f-ranek/moto-beam-driver/electrical/interface_module.kicad_sch

## KiCad design electrical/interface_module.kicad_sch (2024-03-23)

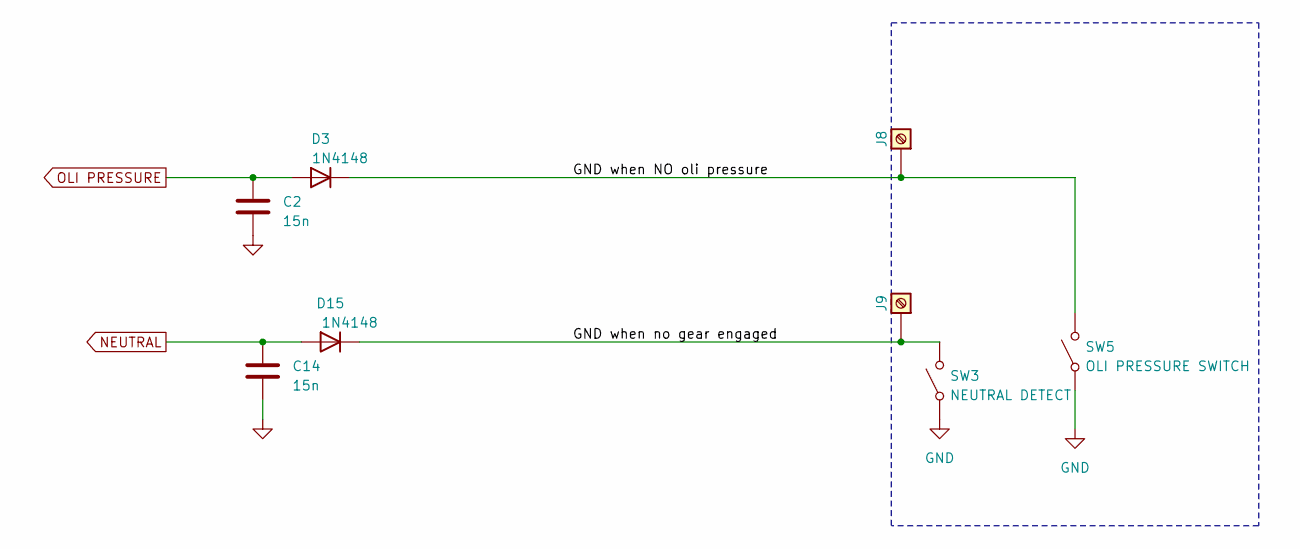
[picture p6: schematic interface_module.kicad_sch]

Parts:
C2, C14: 15n
D3, D15: 1N4148; D_DO-35_SOD27_P7.62mm_Horizontal
J8, J9: Screw_Terminal_01x01
SW3: NEUTRAL DETECT
SW5: OLI PRESSURE SWITCH

Connections:
GND: C2.2, C14.2, SW3.1 (A), SW5.1 (A)
GND when NO oli pressure: D3.1 (K), J8.1, SW5.2 (B)
GND when no gear engaged: D15.1 (K), J9.1, SW3.2 (B)
NEUTRAL: C14.1, D15.2 (A)
OLI PRESSURE: C2.1, D3.2 (A)
