f-ranek/moto-beam-driver/electrical/power_delivery_module.kicad_sch

## KiCad design electrical/power_delivery_module.kicad_sch (2024-04-14)

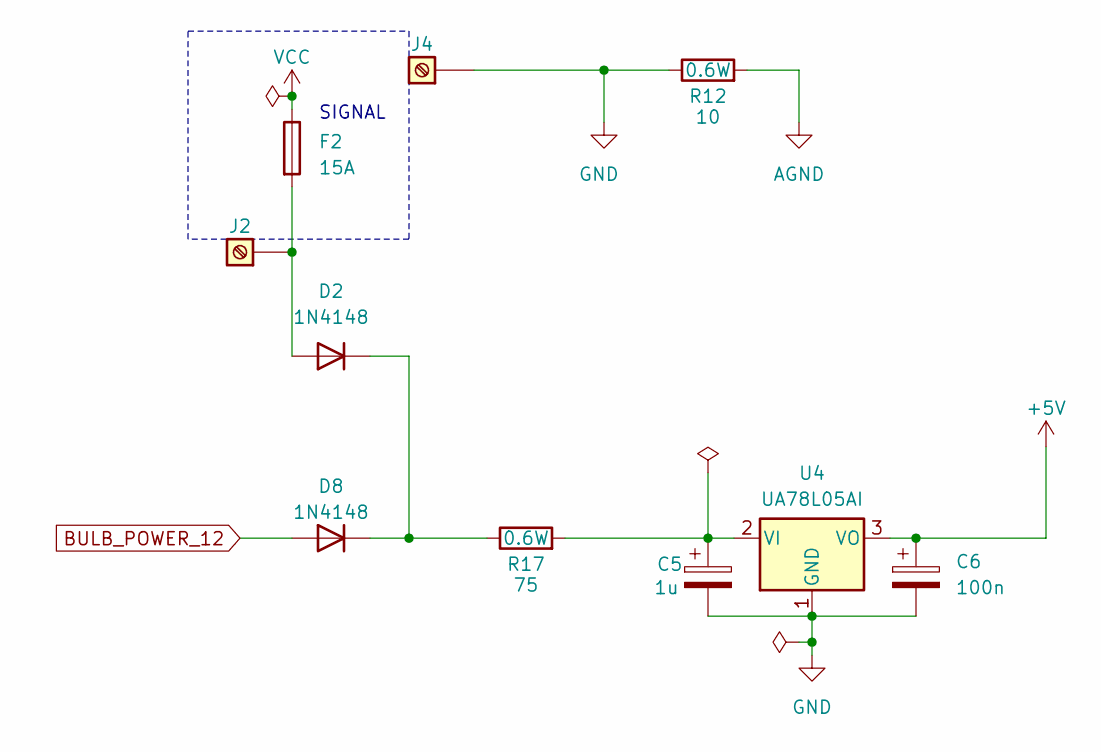
[picture p7: schematic power_delivery_module.kicad_sch]

Parts:
C5: 1u; D_DO-35_SOD27_P7.62mm_Horizontal
C6: 100n; D_DO-35_SOD27_P7.62mm_Horizontal
D2, D8: 1N4148; D_DO-41_SOD81_P10.16mm_Horizontal
F2: 15A
J2, J4: Screw_Terminal_01x01
R12: 10
R17: 75
U4: UA78L05AI; TO-220-3_Vertical

Connections:
+5V: C6.1, U4.3 (VO)
AGND: R12.2
BULB_POWER_12: D8.2 (A)
GND: C5.2, C6.2, J4.1, R12.1, U4.1 (GND)
unnamed: C5.1, R17.2, U4.2 (VI)
unnamed: D2.1 (K), D8.1 (K), R17.1
unnamed: D2.2 (A), F2.2, J2.1
VCC: F2.1

Notes on the sheet:
SIGNAL
