f-ranek/moto-beam-driver/electrical/power_module_n.kicad_sch

## KiCad design electrical/power_module_n.kicad_sch (2024-04-14)

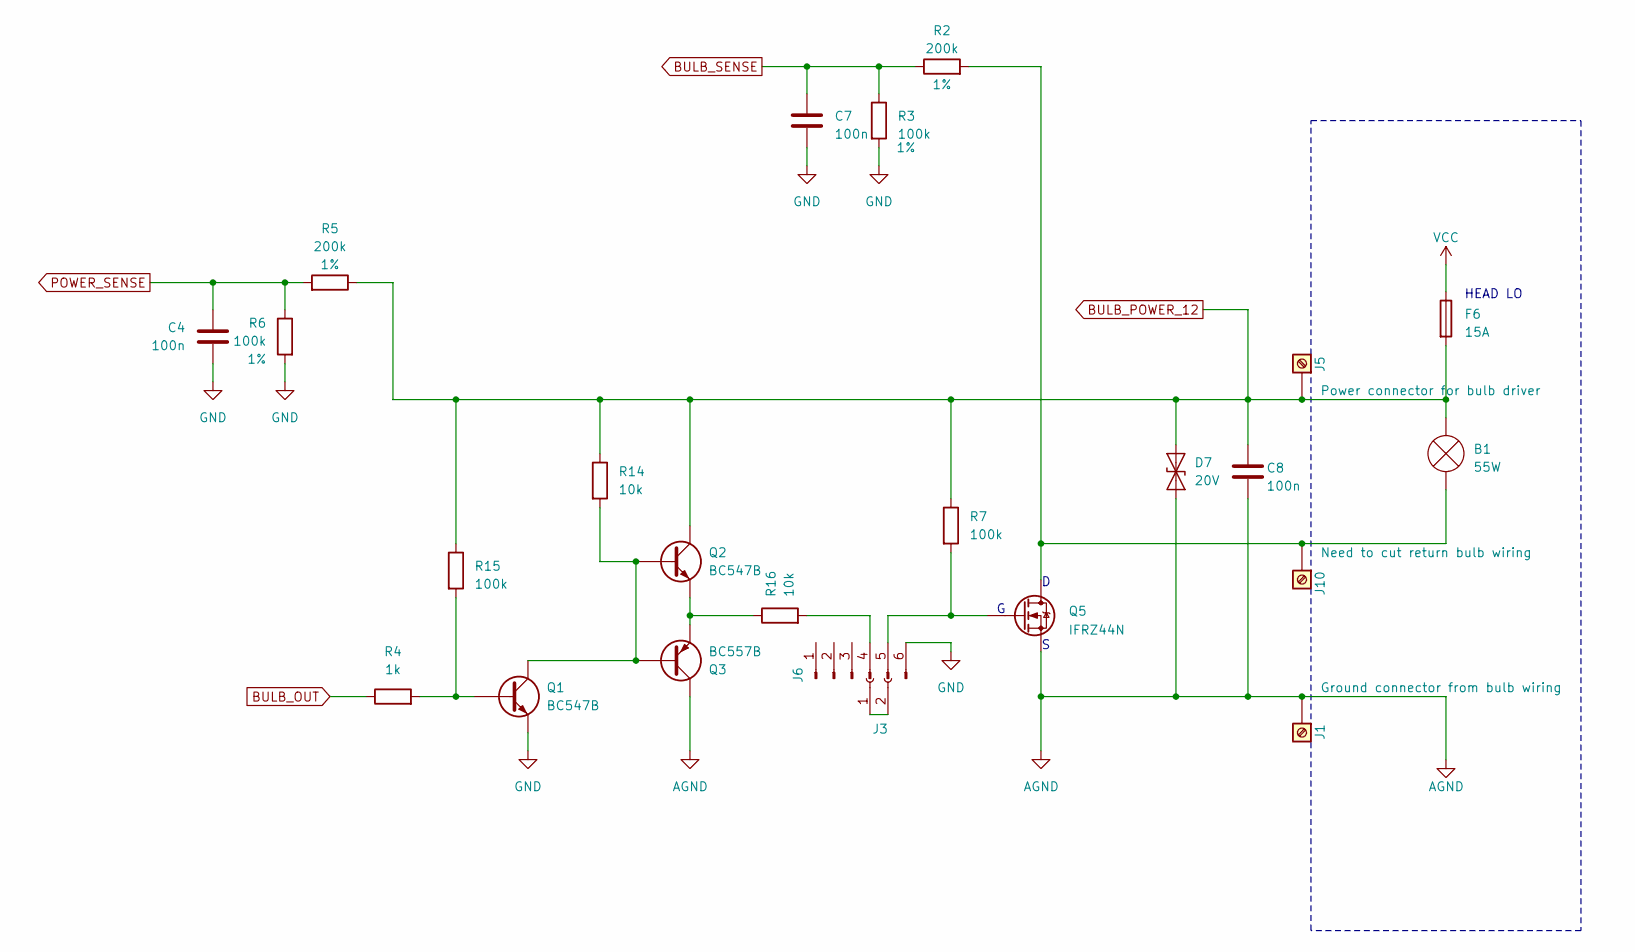
[picture p8: schematic power_module_n.kicad_sch]

Parts:
B1: 55W
C4, C7, C8: 100n
D7: 20V
F6: 15A
J1: Ground connector from bulb wiring
J3: Conn_01x02_Socket
J5: Power connector for bulb driver
J6: Conn_01x06_Pin
J10: Need to cut return bulb wiring
Q1, Q2: BC547B; TO-92_Inline
Q3: BC557B; TO-92_Inline
Q5: IFRZ44N; TO-220-3_Vertical
R2, R5: 200k; Tolerance 1%
R3, R6: 100k; Tolerance 1%
R4: 1k
R7, R15: 100k
R14, R16: 10k

Connections:
AGND: C8.2, D7.1 (A1), J1.1, Q3.1 (C), Q5.3 (S)
BULB_OUT: R4.1
BULB_POWER_12: B1.2 (+), C8.1, D7.2 (A2), F6.2, J5.1, Q2.1 (C), R5.1, R7.1, R14.1, R15.1
BULB_SENSE: C7.1, R2.1, R3.1
GND: C4.2, C7.2, J6.6, Q1.3 (E), R3.2, R6.2
unnamed: B1.1 (-), J10.1, Q5.2 (D), R2.2
unnamed: J3.1, J3.2
unnamed: J6.4, R16.2
unnamed: J6.5, Q5.1 (G), R7.2
unnamed: Q1.1 (C), Q2.2 (B), Q3.2 (B), R14.2
unnamed: Q1.2 (B), R4.2, R15.2
unnamed: Q2.3 (E), Q3.3 (E), R16.1
POWER_SENSE: C4.1, R5.2, R6.1
VCC: F6.1

Notes on the sheet:
HEAD LO
