f-ranek/moto-beam-driver/electrical/power_module_wiring.kicad_sch

## KiCad design electrical/power_module_wiring.kicad_sch (2024-04-14)

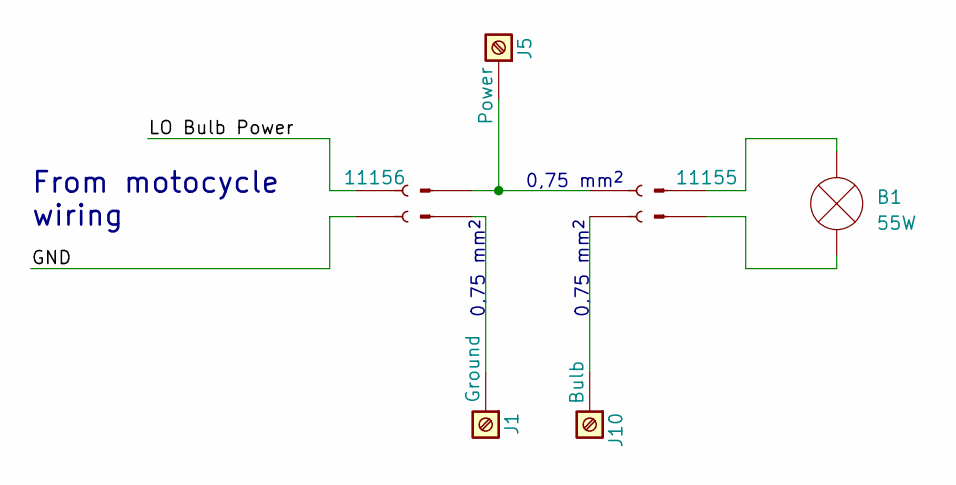
[picture p9: schematic power_module_wiring.kicad_sch]

Parts:
B1: 55W
J1: Ground
J5: Power
J10: Bulb
J12: 11156
J13: Conn_01x02_Pin
J14: Conn_01x02_Socket
J15: 11155

Connections:
GND: J12.2
LO Bulb Power: J12.1
unnamed: B1.1 (-), J15.2
unnamed: B1.2 (+), J15.1
unnamed: J1.1, J13.2
unnamed: J10.1, J14.2
unnamed: J5.1, J13.1, J14.1

Notes on the sheet:
From motocycle wiring
0,75 mm^{2}
