f-ranek/moto-beam-driver/electrical/uc_module.kicad_sch

## KiCad design electrical/uc_module.kicad_sch (2024-04-14)

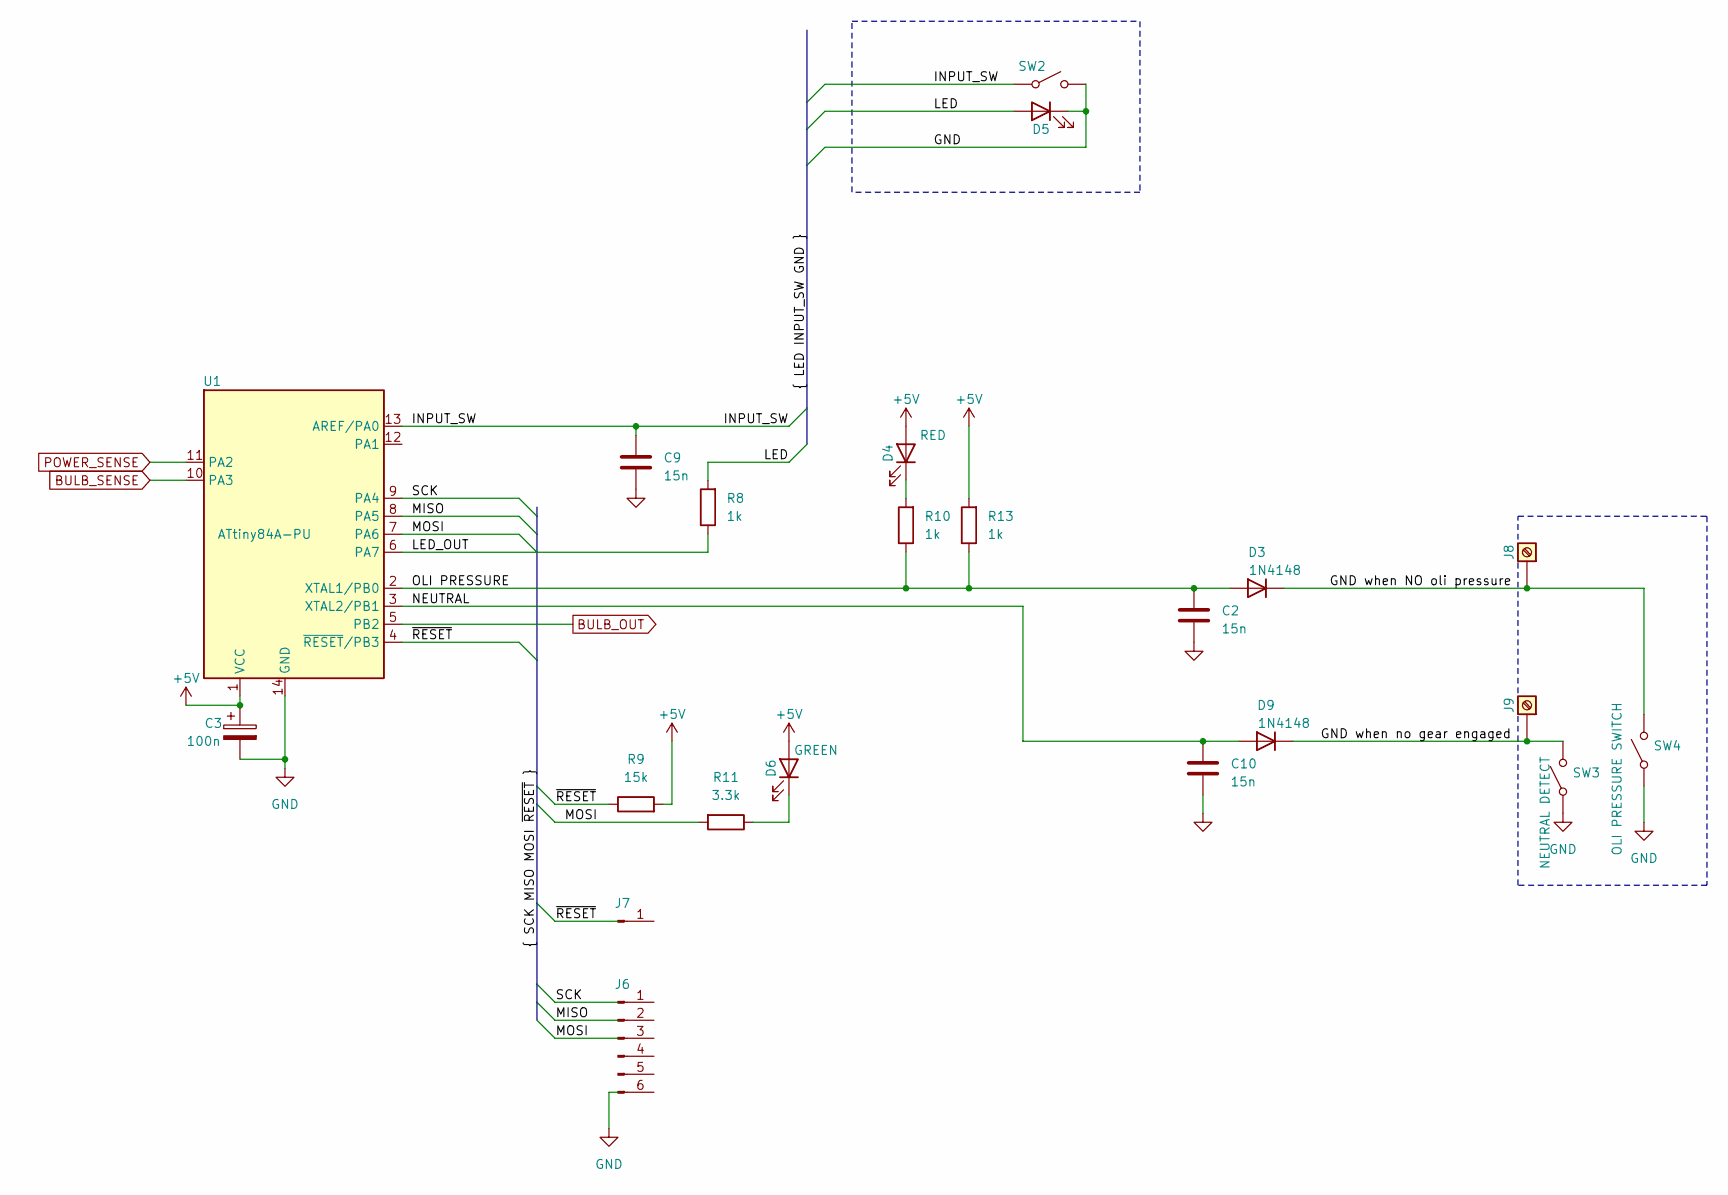
[picture p10: schematic uc_module.kicad_sch]

Parts:
C2, C9, C10: 15n
C3: 100n
D3, D9: 1N4148; D_DO-35_SOD27_P7.62mm_Horizontal
D4: RED
D5: LED
D6: GREEN
J6: Conn_01x06_Pin
J7: Conn_01x01_Pin
J8, J9: Screw_Terminal_01x01
R8, R10, R13: 1k
R9: 15k
R11: 3.3k
SW2: SW_SPST
SW3: NEUTRAL DETECT
SW4: OLI PRESSURE SWITCH
U1: ATtiny84A-PU; DIP-14_W7.62mm

Connections:
+5V: C3.1, D4.2 (A), D6.2 (A), R9.2, R13.2, U1.1 (VCC)
BULB_OUT: U1.5 (PB2)
BULB_SENSE: U1.10 (PA3)
GND: C2.2, C3.2, C9.2, C10.2, D5.1 (K), SW2.2 (B), SW3.1 (A), SW4.1 (A), U1.14 (GND)
GND when NO oli pressure: D3.1 (K), J8.1, SW4.2 (B)
GND when no gear engaged: D9.1 (K), J9.1, SW3.2 (B)
INPUT_SW: C9.1, SW2.1 (A), U1.13 (AREF/PA0)
LED: D5.2 (A), R8.2
LED_OUT: R8.1, U1.6 (PA7)
MISO: U1.8 (PA5)
MOSI: R11.2, U1.7 (PA6)
NEUTRAL: C10.1, D9.2 (A), U1.3 (XTAL2/PB1)
unnamed: D4.1 (K), R10.2
unnamed: D6.1 (K), R11.1
OLI PRESSURE: C2.1, D3.2 (A), R10.1, R13.1, U1.2 (XTAL1/PB0)
POWER_SENSE: U1.11 (PA2)
SCK: U1.9 (PA4)
~RESET: R9.1, U1.4 (~RESET/PB3)
