f-ranek/moto-beam-driver/LED_Drive/app_adc.h

/*
 * app_adc.h
 *
 * Created: 22.03.2024 13:29:54
 *  Author: Bogusław
 */


#ifndef APP_ADC_H_
#define APP_ADC_H_

#include <stdint.h>

#define VOLTAGE_3_V    (0xCF)
#define VOLTAGE_6_V    (0x19D)
#define VOLTAGE_10_V   (0x2B0)
#define VOLTAGE_10_5_V (0x2D3)
#define VOLTAGE_11_5_V (0x318)
#define VOLTAGE_12_5_V (0x35C)
#define VOLTAGE_13_V   (0x37F)
#define VOLTAGE_13_1_V (0x386)
#define VOLTAGE_13_2_V (0x38D)
#define VOLTAGE_13_5_V (0x3A1)
#define VOLTAGE_15_V   (0x3FF)

#define VOLTAGE_0_03_V (0x2)
#define VOLTAGE_0_05_V (0x3)
#define VOLTAGE_0_1_V  (0x7)
#define VOLTAGE_0_5_V  (0x23)

#define BRIGHTENING_TARGET_PWM_VALUE 210

extern void launch_adc();
extern void read_adc_results();

typedef void (*pwm_consumer_t)(uint8_t);

extern void adjust_target_pwm_value(pwm_consumer_t pm_consumer);
extern uint8_t calc_target_pwm_value();

typedef enum __accu_status {
    UNKNOWN,
    // rozrusznik
    STARTER_RUNNING,
    // brak ładowania
    NORMAL,
    // ładowanie
    CHARGING,
} accu_status_e;

extern accu_status_e __accu_status_value;

static inline accu_status_e get_accu_status()
{
    return __accu_status_value;
}

typedef enum __bulb_actual_status {
    // do 3V, normalna praca
    BULB_VOLTAGE_UNDER_LOAD,

    // powyżej 10 V, wszystko ok, żarówka wyłączona
    BULB_VOLTAGE_FULL,

    // blisko zero V, przepalona żarówka lub bezpiczenik
    BULB_VOLTAGE_ZERO,

    BULB_VOLTAGE_UNKNOWN_READING
} bulb_actual_status_e;

extern bulb_actual_status_e get_bulb_actual_status();

#endif /* APP_ADC_H_ */
