f-ranek/moto-beam-driver/LED_Drive/morse.h

/*
 * morse.h
 *
 * Created: 23.03.2024 21:38:20
 *  Author: Bogusław
 */


#ifndef MORSE_H_
#define MORSE_H_

// emituje kod morse zmapowany ze status_code
void emmit_morse_status_code_if_ready(uint8_t status_code);

#endif /* MORSE_H_ */
