f-ranek/moto-beam-driver/LED_Drive/spi.h

/*
 * spi.h
 *
 * Created: 09.03.2024 23:02:21
 *  Author: Bogusław
 */


#ifndef SPI_H_
#define SPI_H_

#include <stddef.h>

extern void emmit_spi_data(void* data, uint8_t size);

#endif /* SPI_H_ */
